psk7/scorpion-card-pub/revC-mikka/atmega/src/USBHost/HIDParser.cpp

/*
             LUFA Library
     Copyright (C) Dean Camera, 2021.

  dean [at] fourwalledcubicle [dot] com
           www.lufa-lib.org
*/

/*
  Copyright 2021  Dean Camera (dean [at] fourwalledcubicle [dot] com)

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
  The author disclaims all warranties with regard to this
  software, including all implied warranties of merchantability
  and fitness.  In no event shall the author be liable for any
  special, indirect or consequential damages or any damages
  whatsoever resulting from loss of use, data or profits, whether
  in an action of contract, negligence or other tortious action,
  arising out of or in connection with the use or performance of
  this software.
*/

#define  __INCLUDE_FROM_USB_DRIVER
#define  __INCLUDE_FROM_HID_DRIVER

#include "HIDParser.h"
#include "Console.h"
#include "MAX3421.h"

extern "C" unsigned char __heap_start; // NOLINT(bugprone-reserved-identifier)
extern unsigned char *heap_ptr;

USBH::task<uint8_t>
HIDParser::ParseDescriptor(
        USBH::StreamReader<> &Source,
        uint16_t ReportSize, HID_ReportInfo_t *const ParserData) {

    CON << PSTR("HIDParser::ParseDescriptor SP=") << HEX((uint16_t) ((SPH << 8) | SPL)) << PSTR(", Heap ptr=")
        << HEX((uint16_t) heap_ptr) << PSTR(", Heap start=") << HEX((uint16_t) &__heap_start) << endl();

    HID_StateTable_t StateTable[HID_STATETABLE_STACK_DEPTH];
    HID_StateTable_t *CurrStateTable = &StateTable[0];
    HID_CollectionPath_t *CurrCollectionPath = nullptr;
    HID_ReportSizeInfo_t *CurrReportIDInfo = &ParserData->ReportIDSizes[0];
    uint16_t UsageList[HID_USAGE_STACK_DEPTH];
    uint8_t UsageListSize = 0;
    HID_MinMax_t UsageMinMax = {0, 0};

    memset(ParserData, 0x00, sizeof(HID_ReportInfo_t));
    memset(CurrStateTable, 0x00, sizeof(HID_StateTable_t));
    memset(CurrReportIDInfo, 0x00, sizeof(HID_ReportSizeInfo_t));

    ParserData->TotalDeviceReports = 1;

    while (ReportSize) {
        uint8_t HIDReportItem = co_await Source;
        uint32_t ReportItemData;

        ReportSize--;

        switch (HIDReportItem & HID_RI_DATA_SIZE_MASK) {
            case HID_RI_DATA_BITS_32:
                ReportItemData = (uint32_t) co_await Source;
                ReportItemData |= (uint32_t) (co_await Source) << 8;
                ReportItemData |= (uint32_t) (co_await Source) << 16;
                ReportItemData |= (uint32_t) (co_await Source) << 24;
                ReportSize -= 4;
                break;

            case HID_RI_DATA_BITS_16:
                ReportItemData = (uint32_t) co_await Source;
                ReportItemData |= (uint32_t) (co_await Source) << 8;
                ReportSize -= 2;
                break;

            case HID_RI_DATA_BITS_8:
                ReportItemData = (uint32_t) co_await Source;
                ReportSize -= 1;
                break;

            default:
                ReportItemData = 0;
                break;
        }

        switch (HIDReportItem & (HID_RI_TYPE_MASK | HID_RI_TAG_MASK)) {
            case HID_RI_PUSH(0):
                if (CurrStateTable == &StateTable[HID_STATETABLE_STACK_DEPTH - 1])
                    co_return HID_PARSE_HIDStackOverflow;

                memcpy((CurrStateTable + 1),
                       CurrStateTable,
                       sizeof(HID_StateTable_t));

                CurrStateTable++;
                break;

            case HID_RI_POP(0):
                if (CurrStateTable == &StateTable[0])
                    co_return HID_PARSE_HIDStackUnderflow;

                CurrStateTable--;
                break;

            case HID_RI_USAGE_PAGE(0):
                CurrStateTable->Attributes.Usage.Page = ReportItemData;
                break;

            case HID_RI_LOGICAL_MINIMUM(0):
                CurrStateTable->Attributes.Logical.Minimum = ReportItemData;
                break;

            case HID_RI_LOGICAL_MAXIMUM(0):
                CurrStateTable->Attributes.Logical.Maximum = ReportItemData;
                break;

            case HID_RI_PHYSICAL_MINIMUM(0):
                CurrStateTable->Attributes.Physical.Minimum = ReportItemData;
                break;

            case HID_RI_PHYSICAL_MAXIMUM(0):
                CurrStateTable->Attributes.Physical.Maximum = ReportItemData;
                break;

            case HID_RI_UNIT_EXPONENT(0):
                //CurrStateTable->Attributes.Unit.Exponent = ReportItemData;
                break;

            case HID_RI_UNIT(0):
                //CurrStateTable->Attributes.Unit.Type = ReportItemData;
                break;

            case HID_RI_REPORT_SIZE(0):
                CurrStateTable->Attributes.BitSize = ReportItemData;
                break;

            case HID_RI_REPORT_COUNT(0):
                CurrStateTable->ReportCount = ReportItemData;
                break;

            case HID_RI_REPORT_ID(0):
                CurrStateTable->ReportID = ReportItemData;

                if (ParserData->UsingReportIDs) {
                    CurrReportIDInfo = NULL;

                    for (uint8_t i = 0; i < ParserData->TotalDeviceReports; i++) {
                        if (ParserData->ReportIDSizes[i].ReportID == CurrStateTable->ReportID) {
                            CurrReportIDInfo = &ParserData->ReportIDSizes[i];
                            break;
                        }
                    }

                    if (CurrReportIDInfo == NULL) {
                        if (ParserData->TotalDeviceReports == HID_MAX_REPORT_IDS)
                            co_return HID_PARSE_InsufficientReportIDItems;

                        CurrReportIDInfo = &ParserData->ReportIDSizes[ParserData->TotalDeviceReports++];
                        memset(CurrReportIDInfo, 0x00, sizeof(HID_ReportSizeInfo_t));
                    }
                }

                ParserData->UsingReportIDs = true;

                CurrReportIDInfo->ReportID = CurrStateTable->ReportID;
                break;

            case HID_RI_USAGE(0):
                if (UsageListSize == HID_USAGE_STACK_DEPTH)
                    co_return HID_PARSE_UsageListOverflow;

                if ((HIDReportItem & HID_RI_DATA_SIZE_MASK) == HID_RI_DATA_BITS_32)
                    CurrStateTable->Attributes.Usage.Page = (ReportItemData >> 16);

                UsageList[UsageListSize++] = ReportItemData;
                break;

            case HID_RI_USAGE_MINIMUM(0):
                UsageMinMax.Minimum = ReportItemData;
                break;

            case HID_RI_USAGE_MAXIMUM(0):
                UsageMinMax.Maximum = ReportItemData;
                break;

            case HID_RI_COLLECTION(0):
                if (CurrCollectionPath == NULL) {
                    CurrCollectionPath = &ParserData->CollectionPaths[0];
                } else {
                    HID_CollectionPath_t *ParentCollectionPath = CurrCollectionPath;

                    CurrCollectionPath = &ParserData->CollectionPaths[1];

                    while (CurrCollectionPath->Parent != NULL) {
                        if (CurrCollectionPath == &ParserData->CollectionPaths[HID_MAX_COLLECTIONS - 1])
                            co_return HID_PARSE_InsufficientCollectionPaths;

                        CurrCollectionPath++;
                    }

                    CurrCollectionPath->Parent = ParentCollectionPath;
                }

                CurrCollectionPath->Type = ReportItemData;
                CurrCollectionPath->Usage.Page = CurrStateTable->Attributes.Usage.Page;

                if (UsageListSize) {
                    CurrCollectionPath->Usage.Usage = UsageList[0];

                    for (uint8_t i = 1; i < UsageListSize; i++)
                        UsageList[i - 1] = UsageList[i];

                    UsageListSize--;
                } else if (UsageMinMax.Minimum <= UsageMinMax.Maximum) {
                    CurrCollectionPath->Usage.Usage = UsageMinMax.Minimum++;
                }

                break;

            case HID_RI_END_COLLECTION(0):
                if (CurrCollectionPath == NULL)
                    co_return HID_PARSE_UnexpectedEndCollection;

                CurrCollectionPath = CurrCollectionPath->Parent;
                break;

            case HID_RI_INPUT(0):
            case HID_RI_OUTPUT(0):
            case HID_RI_FEATURE(0):
                for (uint8_t ReportItemNum = 0; ReportItemNum < CurrStateTable->ReportCount; ReportItemNum++) {
                    HID_ReportItem_t NewReportItem;

                    memcpy(&NewReportItem.Attributes,
                           &CurrStateTable->Attributes,
                           sizeof(HID_ReportItem_Attributes_t));

                    //NewReportItem.ItemFlags = ReportItemData;
                    NewReportItem.CollectionPath = CurrCollectionPath;
                    NewReportItem.ReportID = CurrStateTable->ReportID;

                    if (UsageListSize) {
                        NewReportItem.Attributes.Usage.Usage = UsageList[0];

                        for (uint8_t i = 1; i < UsageListSize; i++)
                            UsageList[i - 1] = UsageList[i];

                        UsageListSize--;
                    } else if (UsageMinMax.Minimum <= UsageMinMax.Maximum) {
                        NewReportItem.Attributes.Usage.Usage = UsageMinMax.Minimum++;
                    }

                    uint8_t ItemTypeTag = (HIDReportItem & (HID_RI_TYPE_MASK | HID_RI_TAG_MASK));

                    uint8_t ItemType = 0;

                    if (ItemTypeTag == HID_RI_INPUT(0))
                        //NewReportItem.ItemType = HID_REPORT_ITEM_In;
                        ItemType = HID_REPORT_ITEM_In;
                    else if (ItemTypeTag == HID_RI_OUTPUT(0))
                        //NewReportItem.ItemType = HID_REPORT_ITEM_Out;
                        ItemType = HID_REPORT_ITEM_Out;
                    else
                        //NewReportItem.ItemType = HID_REPORT_ITEM_Feature;
                        ItemType = HID_REPORT_ITEM_Feature;

                    //NewReportItem.BitOffset = CurrReportIDInfo->ReportSizeBits[NewReportItem.ItemType];
                    if (ItemType == HID_REPORT_ITEM_In) {
                        NewReportItem.BitOffset = CurrReportIDInfo->ReportSizeBits[ItemType];

                        CurrReportIDInfo->ReportSizeBits[ItemType] += CurrStateTable->Attributes.BitSize;

                        /*ParserData->LargestReportSizeBits = MAX(ParserData->LargestReportSizeBits,
                                                                CurrReportIDInfo->ReportSizeBits[ItemType]);*/
                    }

                    if (!(ReportItemData & HID_IOF_CONSTANT))
                        OnItem(NewReportItem);
                    //ParserData->TotalReportItems++;
                }

                break;

            default:
                break;
        }

        if ((HIDReportItem & HID_RI_TYPE_MASK) == HID_RI_TYPE_MAIN) {
            UsageMinMax.Minimum = 0;
            UsageMinMax.Maximum = 0;
            UsageListSize = 0;
        }
    }

    co_return HID_PARSE_Successful;
}

uint32_t HIDParser::GetItemInfo(const uint8_t *ReportData, HID_ReportItem const &ReportItem, bool SignExtend) {

    uint16_t DataBitsRem = ReportItem.bit_size;
    uint16_t CurrentBit = ReportItem.bit_offset;
    uint32_t BitMask = (1 << 0);

    if (ReportItem.report_id) {
        if (ReportItem.report_id != ReportData[0])
            return 0;

        ReportData++;
    }

    uint32_t value = 0;

    if (SignExtend) {
        uint16_t signBitNum = ReportItem.bit_offset + ReportItem.bit_size - 1;
        uint8_t signBit = (ReportData[signBitNum / 8] & (1 << (signBitNum % 8)));

        value = signBit == 0 ? 0 : ~((1 << ReportItem.bit_size) - 1);
    }

    while (DataBitsRem--) {
        if (ReportData[CurrentBit / 8] & (1 << (CurrentBit % 8)))
            value |= BitMask;

        CurrentBit++;
        BitMask <<= 1;
    }

    return value;
}

uint16_t USB_GetHIDReportSize(HID_ReportInfo_t *const ParserData,
                              const uint8_t ReportID,
                              const uint8_t ReportType) {
    for (uint8_t i = 0; i < HID_MAX_REPORT_IDS; i++) {
        uint16_t ReportSizeBits = ParserData->ReportIDSizes[i].ReportSizeBits[ReportType];

        if (ParserData->ReportIDSizes[i].ReportID == ReportID)
            return (ReportSizeBits / 8) + ((ReportSizeBits % 8) ? 1 : 0);
    }

    return 0;
}

HID_ReportItem::HID_ReportItem(const HID_ReportItem_t &From)
        : bit_offset(From.BitOffset), bit_size(From.Attributes.BitSize), report_id(From.ReportID),
          log_min(From.Attributes.Logical.Minimum), log_max(From.Attributes.Logical.Maximum) {

    auto lMin = From.Attributes.Logical.Minimum;
    auto lMax = From.Attributes.Logical.Maximum;
    auto phMin = From.Attributes.Physical.Minimum;
    auto phMax = From.Attributes.Physical.Maximum;

    if (lMax == lMin)
        k = 1;
    else
        k = (phMax - phMin) / (lMax - lMin);
}
