psk7/scorpion-card-pub/revC-mikka/atmega/src/ZxLayoutLeftShift.cpp

#include "ZxKeyboard.h"
#include "ZxLayout.h"

extern const ZxLayoutKeyRef LeftShiftLayout[256];

const ZxLayoutKeyRef LeftShiftLayout[256] STORAGE = {
        {},
        {},
        {},
        {},
        {},                                                 // HID_KEYBOARD_SC_A
        {},                                                 // HID_KEYBOARD_SC_B
        {},                                                 // HID_KEYBOARD_SC_C
        {},                                                 // HID_KEYBOARD_SC_D
        {},                                                 // HID_KEYBOARD_SC_E
        {},                                                 // HID_KEYBOARD_SC_F
        {},                                                 // HID_KEYBOARD_SC_G
        {},                                                 // HID_KEYBOARD_SC_H
        {},                                                 // HID_KEYBOARD_SC_I
        {},                                                 // HID_KEYBOARD_SC_J
        {},                                                 // HID_KEYBOARD_SC_K
        {},                                                 // HID_KEYBOARD_SC_L
        {},                                                 // HID_KEYBOARD_SC_M
        {},                                                 // HID_KEYBOARD_SC_N
        {},                                                 // HID_KEYBOARD_SC_O
        {},                                                 // HID_KEYBOARD_SC_P
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
        {},
        {},
        {},
        {},
        {},
        {},
        {},
        {},
        {},
        {},
        {},
        {},
        {},
        {},
        {},
        {},
        {},
        {},
        {},
        {},
        {},
        {},
        {},
        {},
};
