psk7/scorpion-card-pub/revC-mikka/atmega/src/USBHost/Common.h

/*
             LUFA Library
     Copyright (C) Dean Camera, 2021.

  dean [at] fourwalledcubicle [dot] com
           www.lufa-lib.org
*/

/*
  Copyright 2021  Dean Camera (dean [at] fourwalledcubicle [dot] com)

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
  The author disclaims all warranties with regard to this
  software, including all implied warranties of merchantability
  and fitness.  In no event shall the author be liable for any
  special, indirect or consequential damages or any damages
  whatsoever resulting from loss of use, data or profits, whether
  in an action of contract, negligence or other tortious action,
  arising out of or in connection with the use or performance of
  this software.
*/

/** \dir
 *  \brief Common library header files.
 *
 *  This folder contains header files which are common to all parts of the LUFA library. They may be used freely in
 *  user applications.
 */

/** \file
 *  \brief Common library convenience headers, macros and functions.
 *
 *  \copydetails Group_Common
 */

/** \defgroup Group_Common Common Utility Headers - LUFA/Drivers/Common/Common.h
 *  \brief Common library convenience headers, macros and functions.
 *
 *  Common utility headers containing macros, functions, enums and types which are common to all
 *  aspects of the library.
 *
 *  @{
 */

/** \defgroup Group_GlobalInt Global Interrupt Macros
 *  \brief Convenience macros for the management of interrupts globally within the device.
 *
 *  Macros and functions to create and control global interrupts within the device.
 */

#ifndef __LUFA_COMMON_H__
#define __LUFA_COMMON_H__

#define ATTR_PACKED
#define ATTR_NON_NULL_PTR_ARG(x)

	/* Macros: */
		#define __INCLUDE_FROM_COMMON_H

	/* Includes: */
		#include <stdint.h>
		#include <stdbool.h>
		#include <string.h>
		#include <stddef.h>

/*
		#include "Architectures.h"
		#include "BoardTypes.h"
		#include "ArchitectureSpecific.h"
		#include "CompilerSpecific.h"
		#include "Attributes.h"
*/

		#if defined(USE_LUFA_CONFIG_HEADER)
			#include "LUFAConfig.h"
		#endif

	/* Enable C linkage for C++ Compilers: */
		#if defined(__cplusplus)
			extern "C" {
		#endif

	/* Public Interface - May be used in end-application: */
		/* Macros: */
			#if !defined(__DOXYGEN__)
				// Obsolete, retained for compatibility with user code
				#define MACROS                  do
				#define MACROE                  while (0)
			#endif

			/** Convenience macro to determine the larger of two values.
			 *
			 *  \attention This macro should only be used with operands that do not have side effects from being evaluated
			 *             multiple times.
			 *
			 *  \param[in] x  First value to compare
			 *  \param[in] y  First value to compare
			 *
			 *  \return The larger of the two input parameters
			 */
			#if !defined(MAX) || defined(__DOXYGEN__)
				#define MAX(x, y)               (((x) > (y)) ? (x) : (y))
			#endif

			/** Convenience macro to determine the smaller of two values.
			 *
			 *  \attention This macro should only be used with operands that do not have side effects from being evaluated
			 *             multiple times.
			 *
			 *  \param[in] x  First value to compare.
			 *  \param[in] y  First value to compare.
			 *
			 *  \return The smaller of the two input parameters
			 */
			#if !defined(MIN) || defined(__DOXYGEN__)
				#define MIN(x, y)               (((x) < (y)) ? (x) : (y))
			#endif

			#if !defined(STRINGIFY) || defined(__DOXYGEN__)
				/** Converts the given input into a string, via the C Preprocessor. This macro puts literal quotation
				 *  marks around the input, converting the source into a string literal.
				 *
				 *  \param[in] x  Input to convert into a string literal.
				 *
				 *  \return String version of the input.
				 */
				#define STRINGIFY(x)            #x

				/** Converts the given input into a string after macro expansion, via the C Preprocessor. This macro puts
				 *  literal quotation marks around the expanded input, converting the source into a string literal.
				 *
				 *  \param[in] x  Input to expand and convert into a string literal.
				 *
				 *  \return String version of the expanded input.
				 */
				#define STRINGIFY_EXPANDED(x)   STRINGIFY(x)
			#endif

			#if !defined(CONCAT) || defined(__DOXYGEN__)
				/** Concatenates the given input into a single token, via the C Preprocessor.
				 *
				 *  \param[in] x  First item to concatenate.
				 *  \param[in] y  Second item to concatenate.
				 *
				 *  \return Concatenated version of the input.
				 */
				#define CONCAT(x, y)            x ## y

				/** CConcatenates the given input into a single token after macro expansion, via the C Preprocessor.
				 *
				 *  \param[in] x  First item to concatenate.
				 *  \param[in] y  Second item to concatenate.
				 *
				 *  \return Concatenated version of the expanded input.
				 */
				#define CONCAT_EXPANDED(x, y)   CONCAT(x, y)
			#endif

			#if !defined(ISR) || defined(__DOXYGEN__)
				/** Macro for the definition of interrupt service routines, so that the compiler can insert the required
				 *  prologue and epilogue code to properly manage the interrupt routine without affecting the main thread's
				 *  state with unintentional side-effects.
				 *
				 *  Interrupt handlers written using this macro may still need to be registered with the microcontroller's
				 *  Interrupt Controller (if present) before they will properly handle incoming interrupt events.
				 *
				 *  \note This macro is only supplied on some architectures, where the standard library does not include a valid
				 *        definition. If an existing definition exists, the alternative definition here will be ignored.
				 *
				 *  \ingroup Group_GlobalInt
				 *
				 *  \param[in] Name  Unique name of the interrupt service routine.
				 */
				#define ISR(Name, ...)          void Name (void) __attribute__((__interrupt__)) __VA_ARGS__; void Name (void)
			#endif

		/* Inline Functions: */
			/** Function to reverse the individual bits in a byte - i.e. bit 7 is moved to bit 0, bit 6 to bit 1,
			 *  etc.
			 *
			 *  \param[in] Byte  Byte of data whose bits are to be reversed.
			 *
			 *  \return Input data with the individual bits reversed (mirrored).
			 */
			static inline uint8_t BitReverse(uint8_t Byte) ;
			static inline uint8_t BitReverse(uint8_t Byte)
			{
				Byte = (((Byte & 0xF0) >> 4) | ((Byte & 0x0F) << 4));
				Byte = (((Byte & 0xCC) >> 2) | ((Byte & 0x33) << 2));
				Byte = (((Byte & 0xAA) >> 1) | ((Byte & 0x55) << 1));

				return Byte;
			}


	/* Disable C linkage for C++ Compilers: */
		#if defined(__cplusplus)
			}
		#endif

#endif

/** @} */
