psk7/scorpion-card-pub/revC-mikka/atmega/src/USBHost/BootProtocolDriver.h

#ifndef CH_BOOTPROTOCOLDRIVER_H
#define CH_BOOTPROTOCOLDRIVER_H

#include "USBHost.h"

class BootProtocolDriver : public USBH::USBDriver, public USBH::USBTarget {
public:
    bool NewData = false;

    uint8_t interface;

    USBH::task<bool>
    Analyze(USBTarget &Device, uint8_t DeviceClass, const USBH::DescriptorParser &Descriptor) override;

    void Reset() override;

    virtual bool CheckInterface(USB_StdDescriptor_Interface_t *Interface) = 0;
};

#endif //CH_BOOTPROTOCOLDRIVER_H
